jromang/featherstarpointer/openscad/specs/sensors_BNO055_STEMMA_fab_print.png

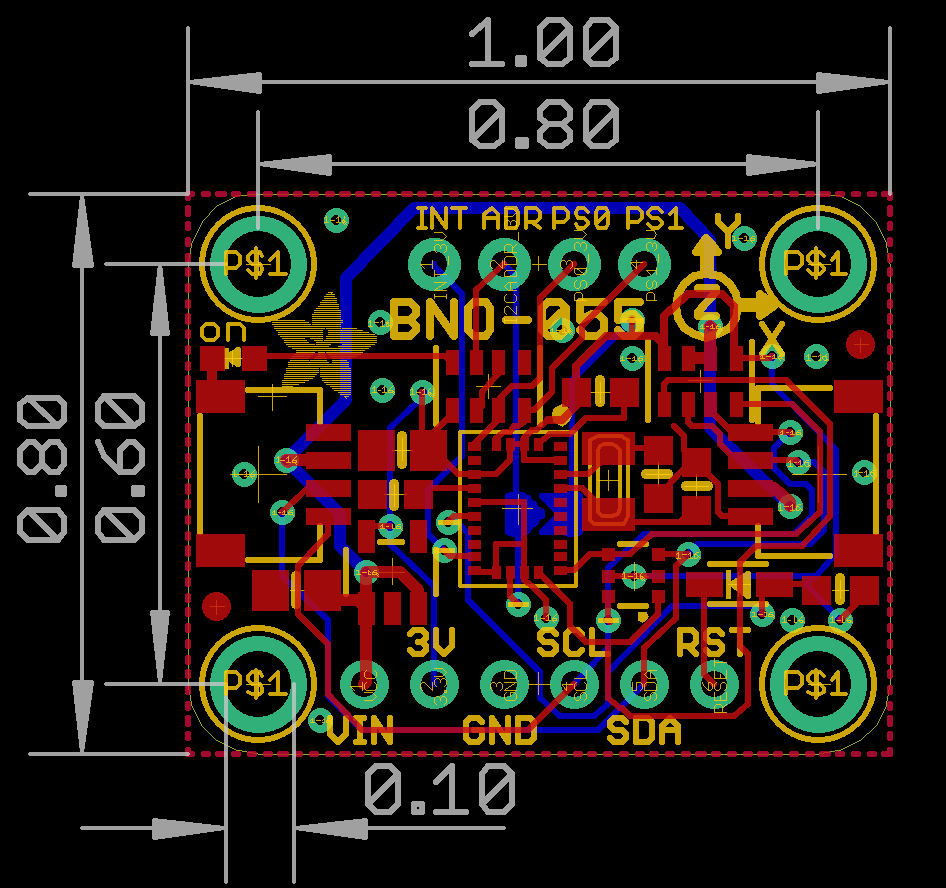
openscad/specs/sensors_BNO055_STEMMA_fab_print.png
